RyanHailey21/neuromorphic-ir-event-sensor/headless_candidate/placement_top.png

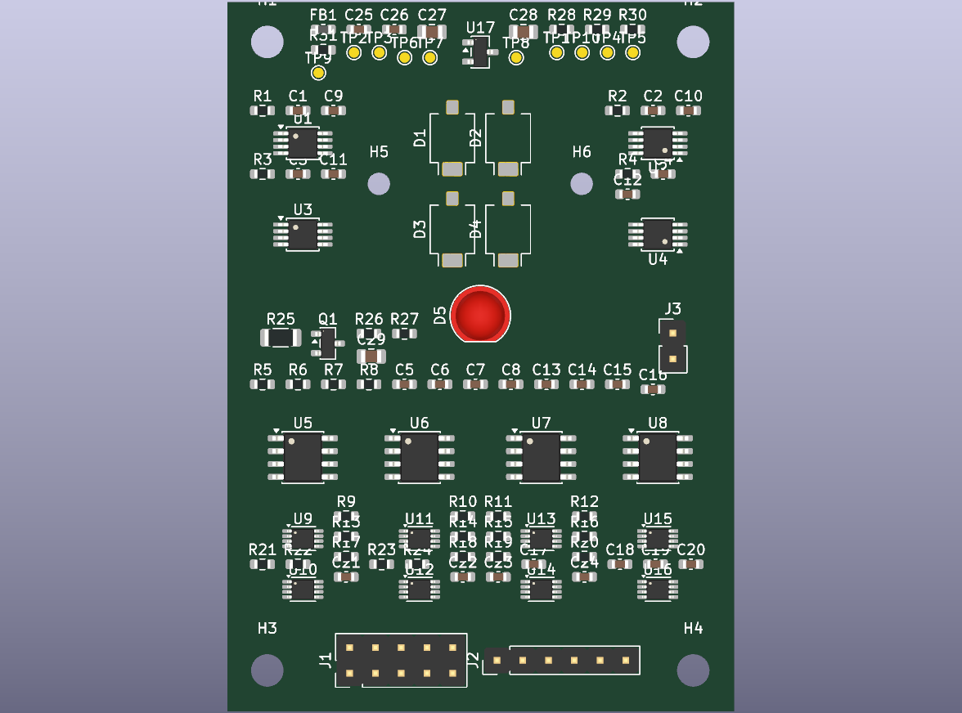
headless_candidate/placement_top.png
