RyanHailey21/neuromorphic-ir-event-sensor/headless_candidate/routed_top.png

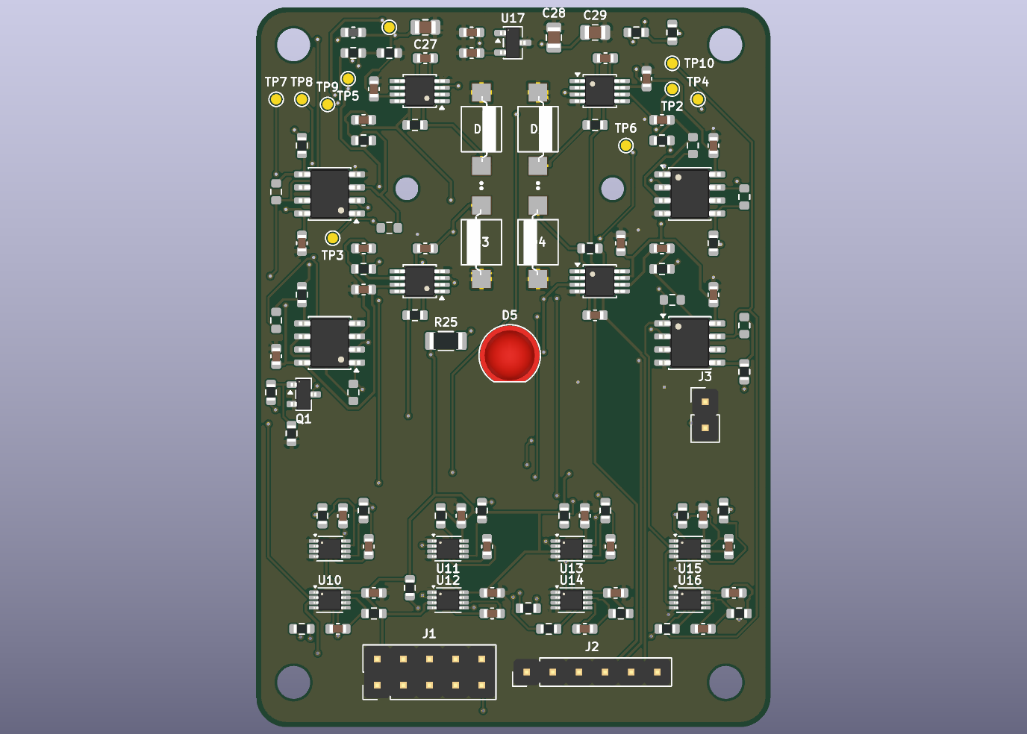
headless_candidate/routed_top.png
