RyanHailey21/neuromorphic-ir-event-sensor/simulation/neuromorphic_afe_spice_bode.png

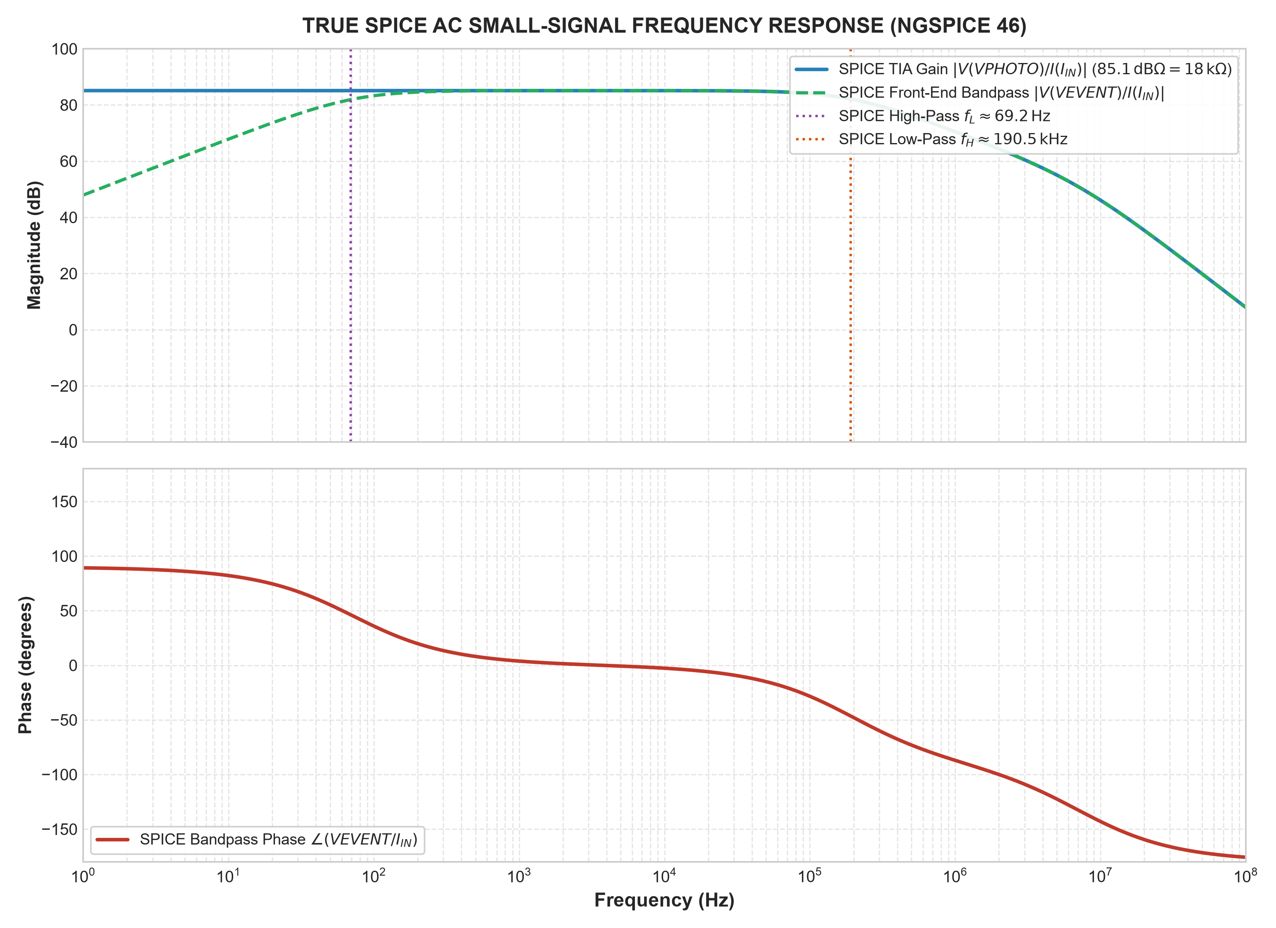
simulation/neuromorphic_afe_spice_bode.png
