RyanHailey21/neuromorphic-ir-event-sensor/simulation/models/scej262/sn74lvc1g123_test.sp

******************************************************************************
* *
* TEXAS INSTRUMENTS INCORPORATED
* Standard Linear and Logic Group
* HSPICE Model for SN74LVC1G123
* PROPERTY OF TEXAS INSTRUMENTS INCORPORATED. UNAUTHORIZED
* REPRODUCTION AND/OR DISTRIBUTION IS STRICTLY PROHIBITED.
*
* THIS PRODUCT IS PROTECTED UNDER COPYRIGHT LAW.
* CREATED 2008, (C) COPYRIGHT 2008, TEXAS INSTRUMENTS
* INCORPORATED, ALL RIGHTS RESERVED
*
* UNLESS THERE IS A SIGNED, WRITTEN AGREEMENT TO THE
* CONTRARY, TEXAS INSTRUMENTS (TI) IS PROVIDING THE IBIS
* MODELS AND WITHOUT ANY WARRANTY, EXPRESSED OR
* IMPLIED. TI ASSUMES NO LIABILITY FOR:
* 1) THE ACCURACY OF THE HSPICE MODELS PROVIDED TO YOUR
* COMPANY;
* 2) THE PROPER FUNCTIONING OF THESE HSPICE MODELS IN YOUR
* DESIGN OR FOR ANY RESULTING APPLICATIONS; OR
* 3) INFRINGEMENT OF PATENTS, COPYRIGHTS OR INTELLECTUAL
* PROPERTY RIGHTS RESULTING FROM YOUR USE OF THESE HSPICE
* MODELS.
*
* TI PROVIDES HSPICE MODELS AS A SERVICE TO OUR CUSTOMERS.
* YOU AND YOUR COMPANY SHALL NOT DISTRIBUTE, SELL OR GIVE
* THESE MODELS TO ANYONE ELSE WITHOUT PRIOR WRITTEN
* PERMISSION FROM TI.
*
* TI RESERVES THE RIGHT TO MAKE CHANGES TO OUR PRODUCTS OR
* TO DISCONTINUE ANY SEMICONDUCTOR PRODUCT OR SERVICE
* WITHOUT NOTICE, AND ADVISES OUR CUSTOMERS TO OBTAIN THE
* LATEST VERSION OF RELEVANT INFORMATION TO VERIFY, BEFORE
* PLACING ORDERS, THAT THE INFORMATION BEING RELIED ON IS
* CURRENT.
*
* PLEASE BE AWARE THAT YOUR RECEIPT AND USE OF THE HSPICE
* INFORMATION PROVIDED SHALL SERVE AS ACCEPTANCE OF THESE
* TERMS AND CONDITIONS. IF YOU DO NOT ACCEPT THESE TERMS,
* YOU SHOULD RETURN OR DESTROY THE HSPICE MODELS AND ANY
* OTHER ACCOMPANYING INFORMATION IMMEDIATELY.
************************************************************************
**** HSPICE EXECUTION OPTIONS ****
************************************************************************
*
.OPTIONS POST $ Enables HSPLOT interface
.OPTIONS ACCT OPTS $ Prints stats & option values used
.OPTIONS SPICE=1 $ Forces Berkeley compatibility
.OPTIONS GMIN=1E-10 $ Lowest allowable conductance values
.OPTIONS GMINDC=1E-10
.OPTIONS ITL1=400 $ Maximum DC iteration limit
.OPTIONS ITL4=40 $ Maximum transient iterations/timestep
.OPTIONS ITL5=0 $ No limit to total transient iterations
***********************************************************************
.OPTIONS search='./'

***********************************************************************
******Top level Subcircuit call (device call)
***********************************************************************
* .INCLUDE 'sn74lvc1g123.inc'
X__SN74LVC1G123 NA B NCLR GND Q CX RX_CX VCC SN74LVC1G123
*** PULSE PARAMETERS ***
.param PFREQ1=10MEG $ 1st pulse (clk) frequency
.param PRFT19=2ns $ rise/fall time
.param PDELAY1=5ns $ delay of 1st pulse
.param PVIN='PVCC' $ input voltage
.param PVT='PVCC/2' $ input threshold voltage
.param PMAX=20ns $ max SPICE delay time
.param PRFT='(PRFT19/0.8)' $ convert rise/fall time to 100$
.param PPD1='(1/PFREQ1)' $ period of 1st pulse
.param PPW1='((PPD1 - (PRFT*2))/2)' $ pulse width of 1st pulse

*** TRANSIENT START & START PARAMETERS ***
.param PSTART='PDELAY1' $ time input starts to transition.
.param PSTOP='PSTART+80n' $
.TRAN 0.1n 'PSTOP' 'PSTART' 0.1n
.PRINT TRAN v(Q)

* SET CONTROL INPUTS TO ENABLE OUTPUT
VC0 NA 0 DC 0
VC1 NCLR 0 DC 'PVCC'


*** SET INPUT AND TEST OUTPUT TO GO LOW ****
VI0 B 0 pulse 'PVIN' 0 'PDELAY1' 'PRFT' 'PRFT' 18n 40n


* CHANGE TO THE OUTPUT NODE
RLOAD  Q     0      500
CLOAD  Q     0      50pF
CEXT   RX_CX CX     28pF
REXT   VCC   RX_CX  2k
VCEXT  CX    0      DC 0V


* VOLTAGE SUPPLIES
vnc nc 0 0
rnc nc 0 1

.param PVCC=5.0
.param PGND=0v
VVCC VCC 0 'PVCC'
VGND GND 0 'PGND'

.TEMP 40

* RESISTORS TO PREVENT DANGLING NODES
* R1G_1 NA 0 1G
* R1G_2 B 0 1G
* R1G_3 NCLR 0 1G
* R1G_4 GND 0 1G
* R1G_5 Q 0 1G
* R1G_6 CX 0 1G
* R1G_7 RX_CX 0 1G
* R1G_8 VCC 0 1G

.END
