RyanHailey21/neuromorphic-ir-event-sensor/simulation/models/sbombt6/TLV3201-PSpiceFiles/SCHEMATIC1/test1/test1.cir

** Profile: "SCHEMATIC1-test1"  [ C:\Modeling\TLV3201_ti\TLV3201-PSpiceFiles\SCHEMATIC1\test1.sim ] 

** Creating circuit file "test1.cir" 
** WARNING: THIS AUTOMATICALLY GENERATED FILE MAY BE OVERWRITTEN BY SUBSEQUENT SIMULATIONS

*Libraries: 
* Profile Libraries :
* Local Libraries :
.LIB "../../../tlv3201.lib" 
* From [PSPICE NETLIST] section of C:\SPB_DATA\cdssetup\OrCAD_PSpice\17.4.0\PSpice.ini file:
.lib "nom.lib" 

*Analysis directives: 
.TRAN  0 5u 0 
.OPTIONS ADVCONV
.PROBE64 V(alias(*)) I(alias(*)) W(alias(*)) D(alias(*)) NOISE(alias(*)) 
.INC "..\SCHEMATIC1.net" 


.END
