RyanHailey21/neuromorphic-ir-event-sensor/simulation/models/sboj021/TLV3202_Q1zip/TLV3202_Q1-PSpiceFiles/TLV3202_Q1/test4/test4.cir

** Profile: "TLV3202_Q1-test4"  [ C:\Users\a0227287\Documents\TLV3202_Q1\TLV3202_Q1-PSpiceFiles\TLV3202_Q1\test4.sim ] 

** Creating circuit file "test4.cir" 
** WARNING: THIS AUTOMATICALLY GENERATED FILE MAY BE OVERWRITTEN BY SUBSEQUENT SIMULATIONS

*Libraries: 
* Profile Libraries :
* Local Libraries :
.LIB "../../../tlv3202_q1-pspicefiles/subcircuit.lib" 
* From [PSPICE NETLIST] section of C:\Users\a0227287\AppData\Roaming\SPB_Data\cdssetup\OrCAD_PSpice/16.6.0/PSpice.ini file:
.lib "nom.lib" 

*Analysis directives: 
.TRAN  0 200ns 0 200p 
.OPTIONS ADVCONV
.PROBE64 V(alias(*)) I(alias(*)) W(alias(*)) D(alias(*)) NOISE(alias(*)) 
.INC "..\TLV3202_Q1.net" 


.END
